tomacha/Room-thermostat-and-relay-module-with-MQTT-protocol/Code/stm32/Thermostat/Core/Inc/ds18b20Config.h

#ifndef	_DS18B20CONFIG_H
#define	_DS18B20CONFIG_H


//	Init timer on cube    1us per tick				example 72 MHz cpu >>> Prescaler=(72-1)      counter period=Max 
//###################################################################################
#define	_DS18B20_USE_FREERTOS		    				0
#define _DS18B20_MAX_SENSORS		    				1
#define	_DS18B20_GPIO												DS18B20_GPIO_Port
#define	_DS18B20_PIN												DS18B20_Pin

#define	_DS18B20_CONVERT_TIMEOUT_MS					5000
#if (_DS18B20_USE_FREERTOS==1)
#define	_DS18B20_UPDATE_INTERVAL_MS					10000					//  (((	if==0  >> Ds18b20_ManualConvert()  )))    ((( if>0  >>>> Auto refresh ))) 
#endif


#define	_DS18B20_TIMER											htim6
//###################################################################################

//#define DS18B20_USE_CRC 1

#endif
